sbarabe/SBK_WRISTBLASTER/images/Arm braced 24seg BarMeter PowerCell Battery pack holder (2).jpg

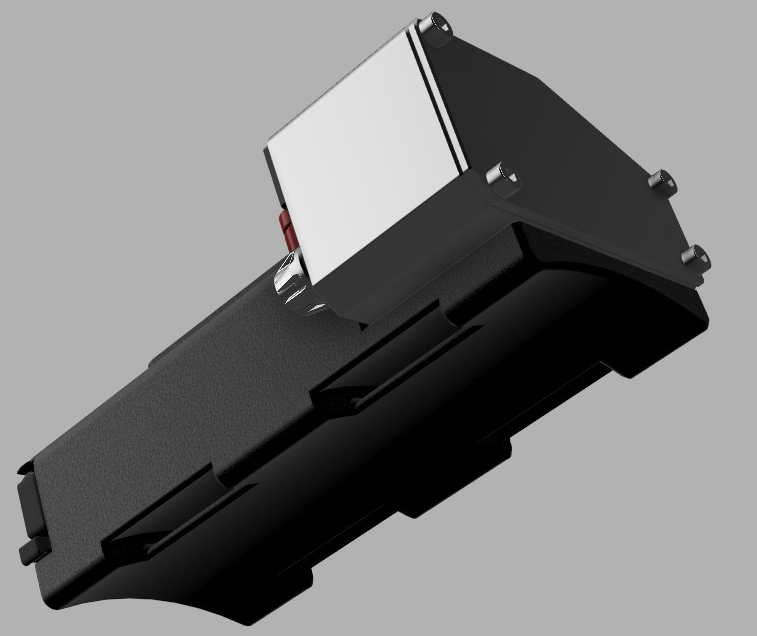
images/Arm braced 24seg BarMeter PowerCell Battery pack holder (2).jpg
