sbarabe/SBK_WRISTBLASTER/Schematics/SBK PCBs/SBK BarDrive SA28 V2.png

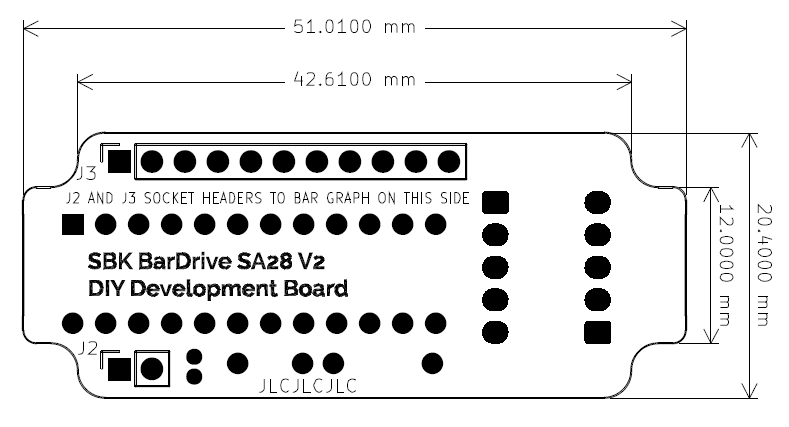
Schematics/SBK PCBs/SBK BarDrive SA28 V2.png
