sbarabe/SBK_WRISTBLASTER/Schematics/SBK PCBs/SBK BarDriveHT 28 V2.png

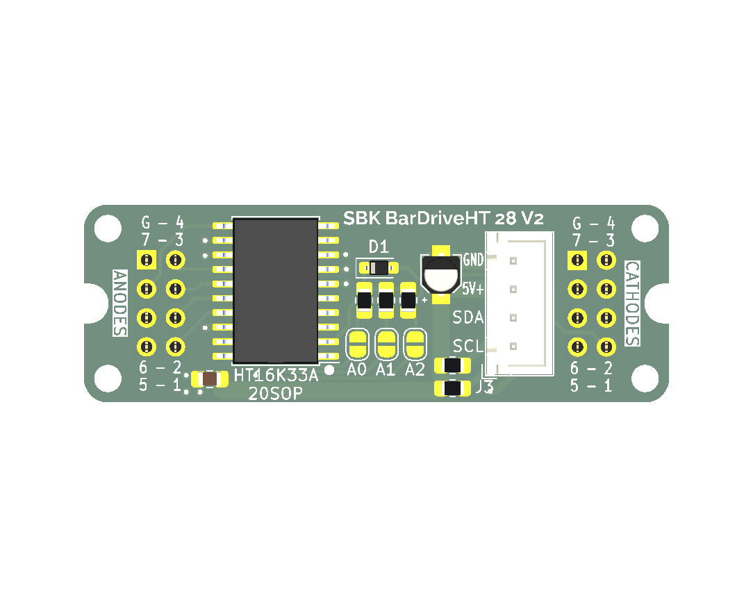
Schematics/SBK PCBs/SBK BarDriveHT 28 V2.png
