sbarabe/SBK_WRISTBLASTER/Schematics/SBK PCBs/SBK BarMeter SA28 V1.png

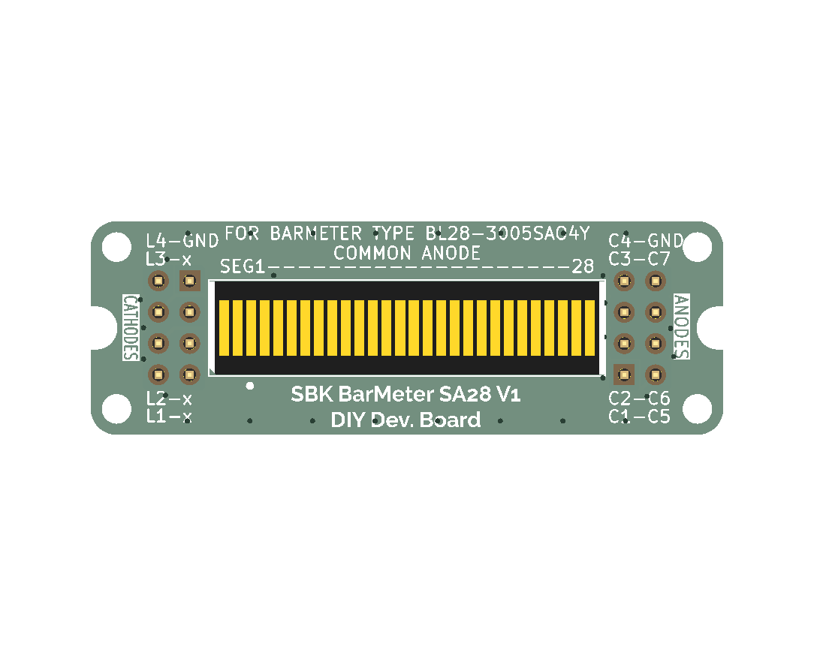
Schematics/SBK PCBs/SBK BarMeter SA28 V1.png
