sbarabe/SBK_WRISTBLASTER/3D model/V1 - 20250310/02.3-Gunbox Bar graph support.stl

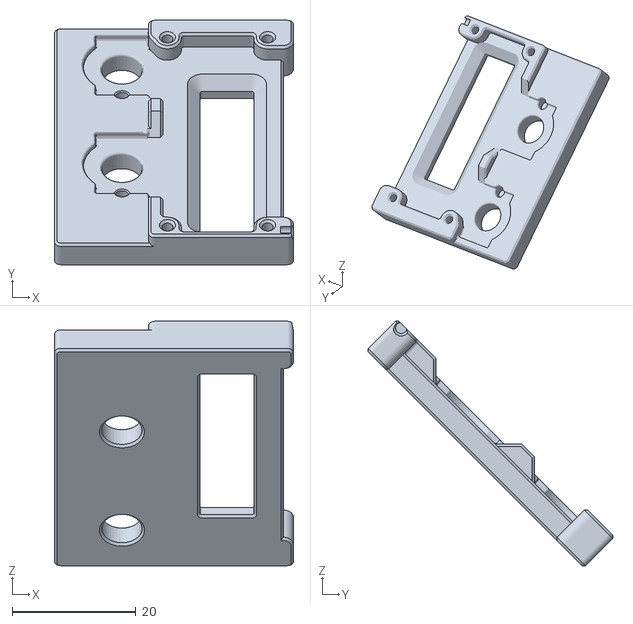
[picture p34: CAD file, 2025-04-01]
3D model/V1 - 20250310/02.3-Gunbox Bar graph support.stl
38.7 x 39.6 x 39.6
