sbarabe/SBK_WRISTBLASTER/3D model/V2 - 20260806/17A-Clippart valve body.stl

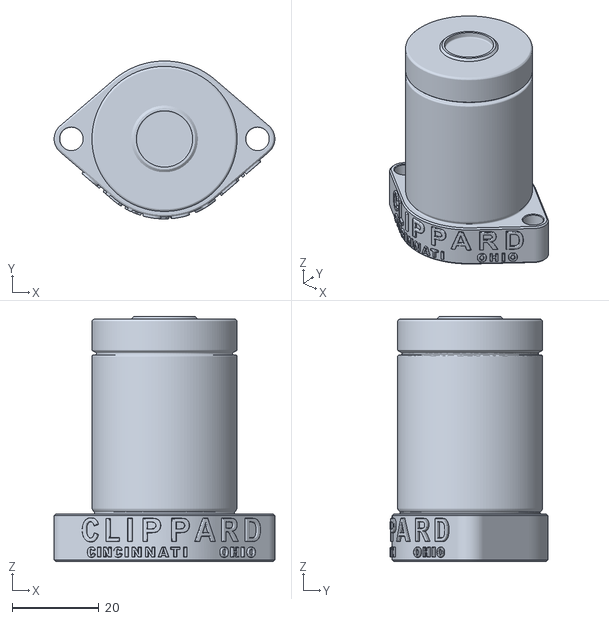
[picture p35: CAD file, 2026-08-06]
3D model/V2 - 20260806/17A-Clippart valve body.stl
51.0 x 36.5 x 56.6
