sbarabe/SBK_WRISTBLASTER/3D model/Battery pack holders/31.2B Battery pack holder COVER.stl

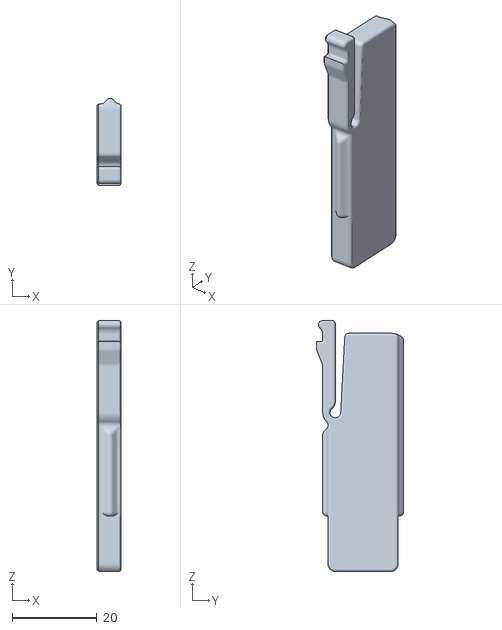
[picture p36: CAD file, 2025-04-04]
3D model/Battery pack holders/31.2B Battery pack holder COVER.stl
5.70 x 20.6 x 59.3
