sbarabe/SBK_WRISTBLASTER/3D model/V1 - 20250310/02-Gunbox ONE PIECE.stl

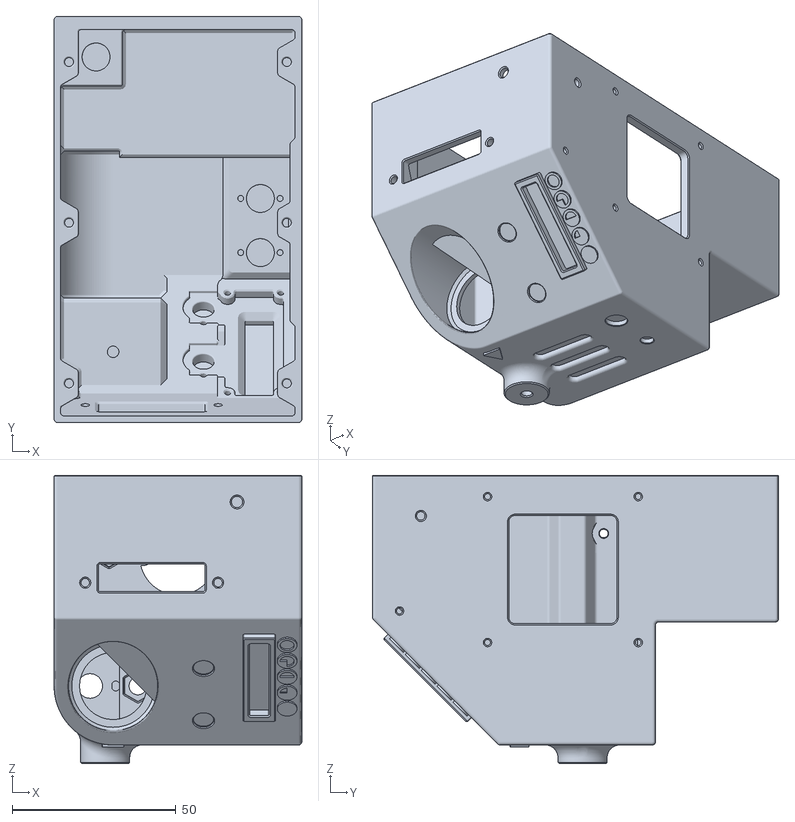
[picture p37: CAD file, 2025-03-19]
3D model/V1 - 20250310/02-Gunbox ONE PIECE.stl
75.6 x 123.8 x 87.9
