sbarabe/SBK_WRISTBLASTER/3D model/V2 - 20260806/18A-Clippart valve knob.stl

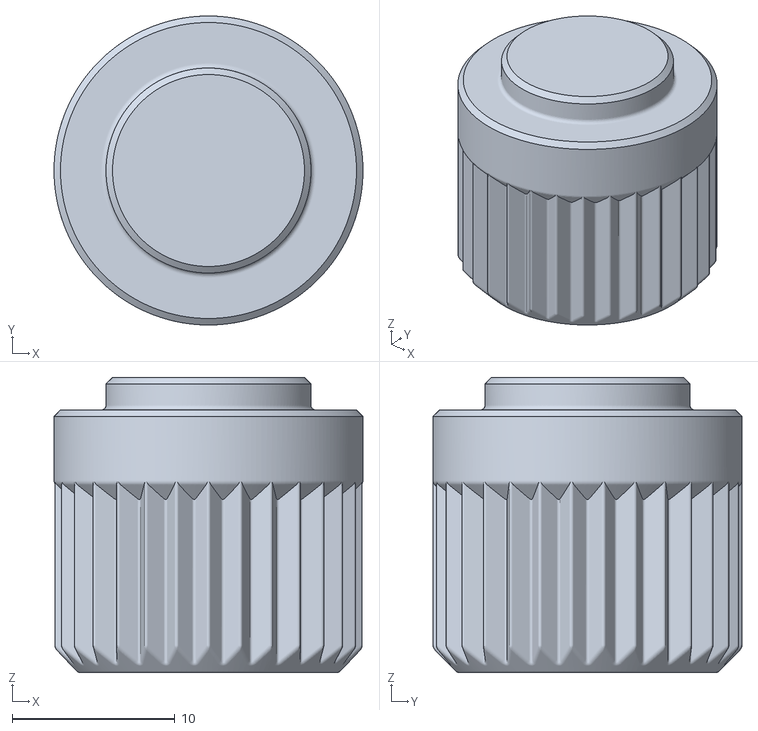
[picture p38: CAD file, 2026-08-06]
3D model/V2 - 20260806/18A-Clippart valve knob.stl
19.0 x 19.0 x 18.2
