sbarabe/SBK_WRISTBLASTER/3D model/Battery pack holders/31.4B_C Cable gland.stl

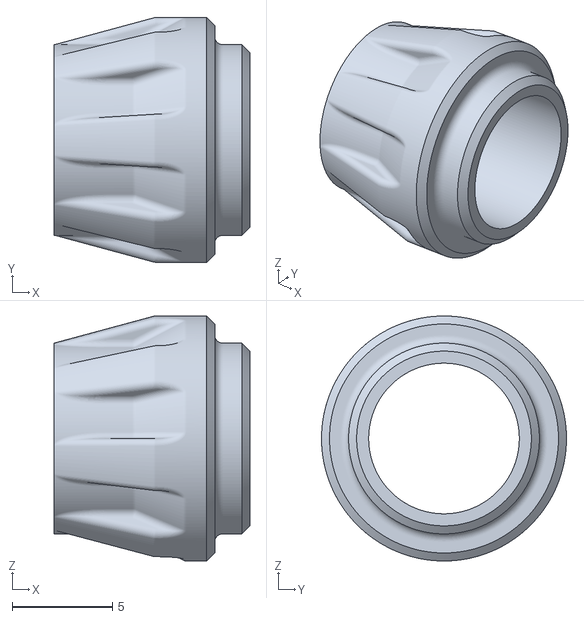
[picture p39: CAD file, 2025-04-04]
3D model/Battery pack holders/31.4B_C Cable gland.stl
9.75 x 12.2 x 12.2
