sbarabe/SBK_WRISTBLASTER/3D model/V1 - 20250310/02.1-Gunbox.stl

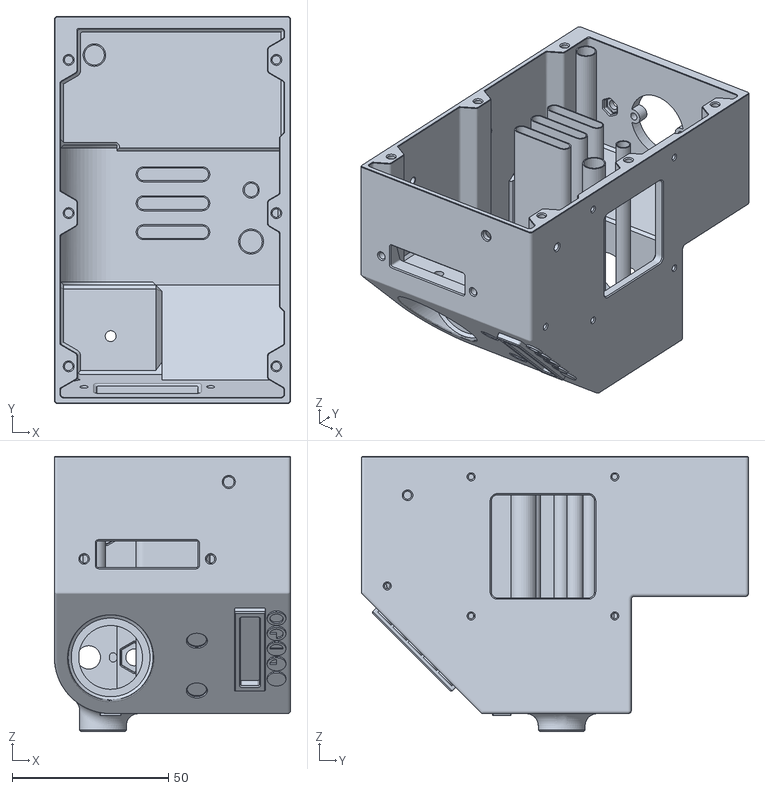
[picture p40: CAD file, 2025-03-12]
3D model/V1 - 20250310/02.1-Gunbox.stl
75.6 x 123.8 x 87.9
