sbarabe/SBK_WRISTBLASTER/3D model/V1 - 20250310/25B-Fire Handle body .375 copper tube.stl

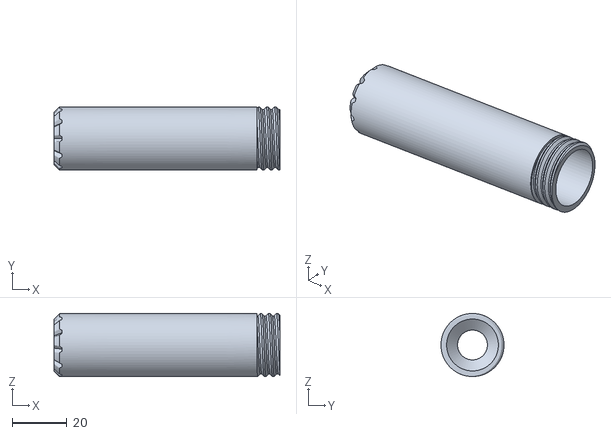
[picture p41: CAD file, 2025-03-10]
3D model/V1 - 20250310/25B-Fire Handle body .375 copper tube.stl
82.8 x 23.1 x 23.1
