sbarabe/SBK_WRISTBLASTER/3D model/V2 - 20260806/18B-Clippart valve knob for potentiometer V2.stl

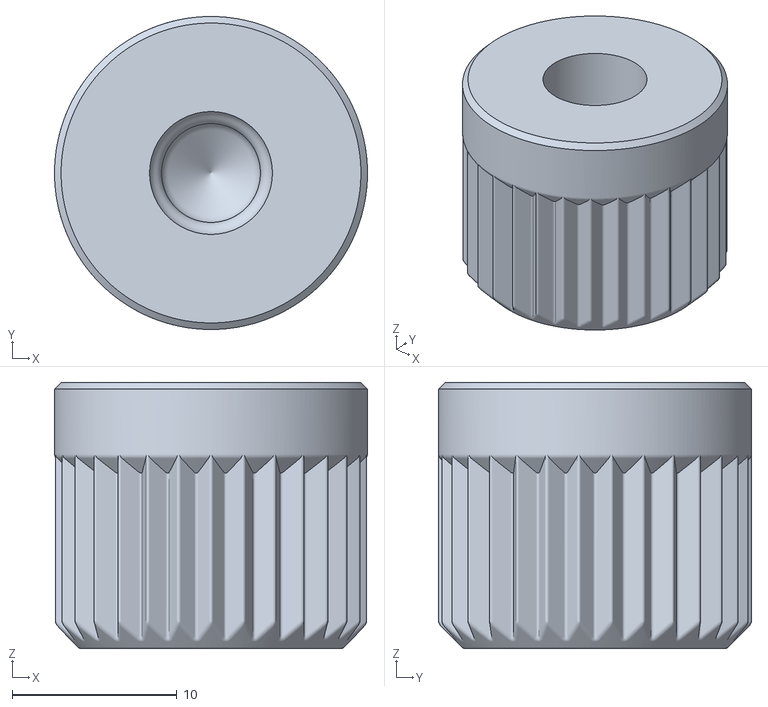
[picture p42: CAD file, 2026-08-06]
3D model/V2 - 20260806/18B-Clippart valve knob for potentiometer V2.stl
19.0 x 19.0 x 16.2
