sbarabe/SBK_WRISTBLASTER/3D model/Battery pack holders/31.3B Powercell switch back cover.stl

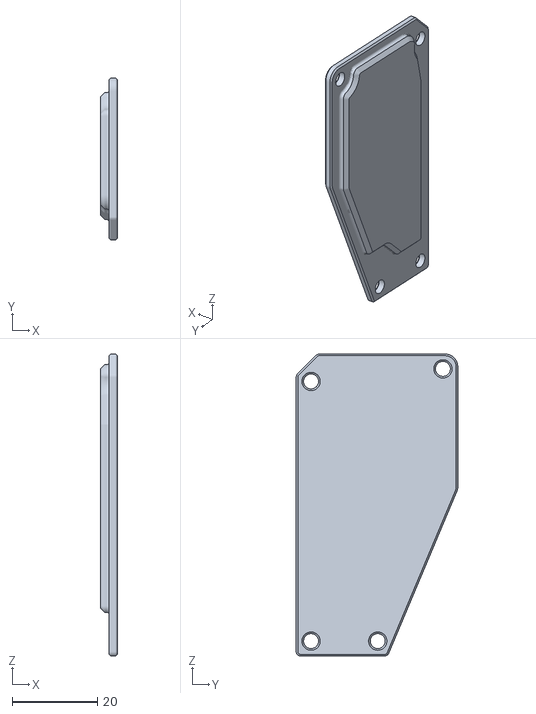
[picture p43: CAD file, 2025-04-04]
3D model/Battery pack holders/31.3B Powercell switch back cover.stl
4.00 x 38.0 x 71.0
