sbarabe/SBK_WRISTBLASTER/3D model/V1 - 20250310/02.2-Gunbox top indicators leds support.stl

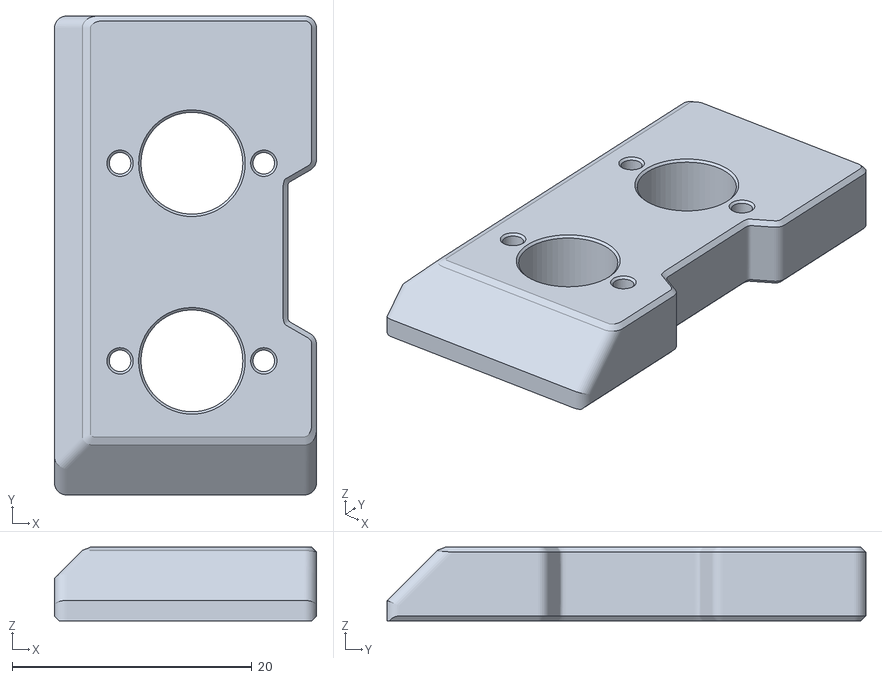
[picture p44: CAD file, 2025-03-10]
3D model/V1 - 20250310/02.2-Gunbox top indicators leds support.stl
21.9 x 40.0 x 6.15
