sbarabe/SBK_WRISTBLASTER/3D model/V2 - 20260806/17B-Clippart valve body for potentiometer V2.stl

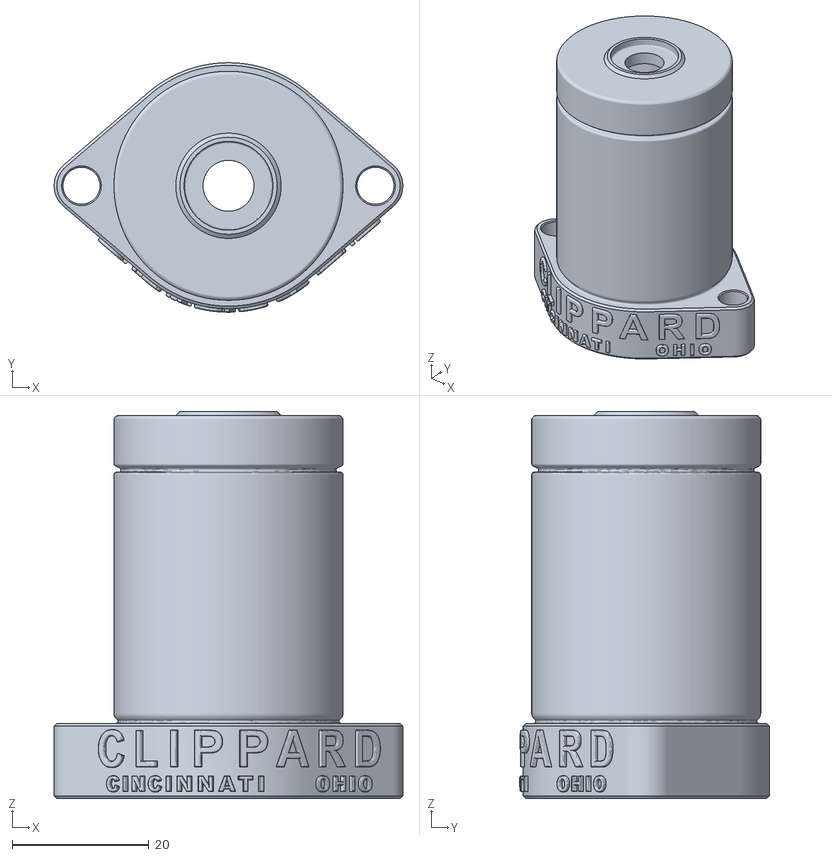
[picture p45: CAD file, 2026-08-06]
3D model/V2 - 20260806/17B-Clippart valve body for potentiometer V2.stl
51.0 x 36.5 x 56.6
