sbarabe/SBK_WRISTBLASTER/3D model/Battery pack holders/31.6B Powercell 9x57x2mm lens (clear or frosted acrylic, not to be printed).stl

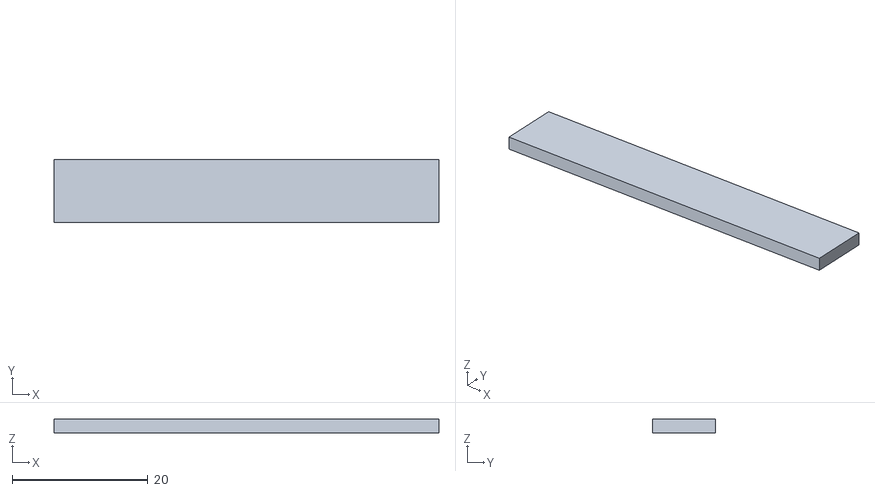
[picture p46: CAD file, 2025-03-24]
3D model/Battery pack holders/31.6B Powercell 9x57x2mm lens (clear or frosted acrylic, not to be printed).stl
56.8 x 9.30 x 2.00
