sbarabe/SBK_WRISTBLASTER/3D model/V2 - 20260806/04-Arm brace LARGE V2 - one side version.stl

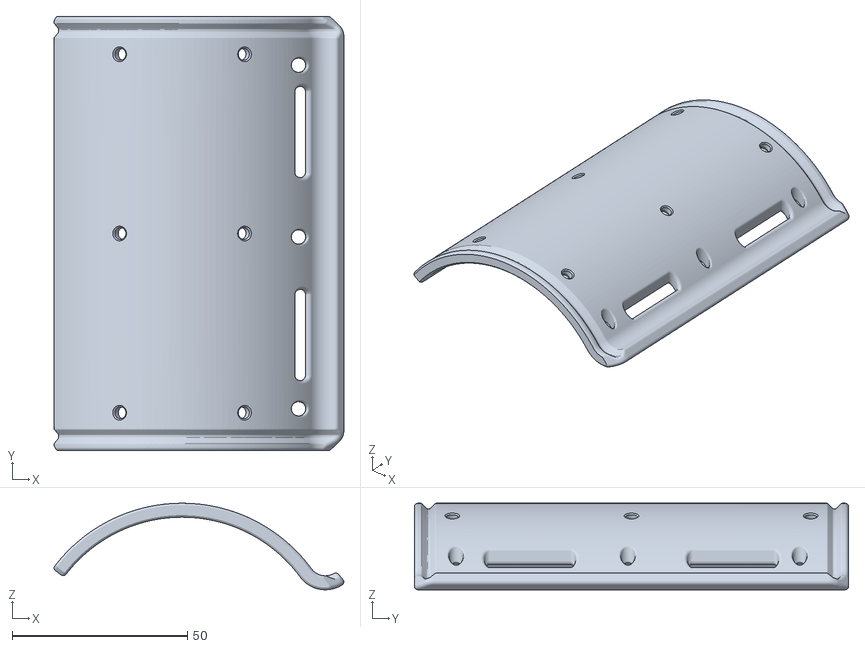
[picture p47: CAD file, 2026-08-06]
3D model/V2 - 20260806/04-Arm brace LARGE V2 - one side version.stl
82.6 x 123.8 x 24.7
