sbarabe/SBK_WRISTBLASTER/3D model/V1 - 20250310/02.4-Gunbox Front indicator led support.stl

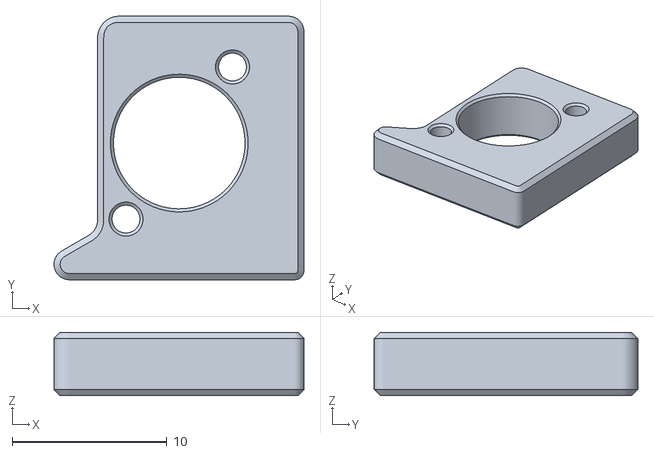
[picture p48: CAD file, 2025-03-10]
3D model/V1 - 20250310/02.4-Gunbox Front indicator led support.stl
16.2 x 17.0 x 4.10
