sbarabe/SBK_WRISTBLASTER/3D model/V2 - 20260806/04-Arm brace LARGE V2 - symetric.stl

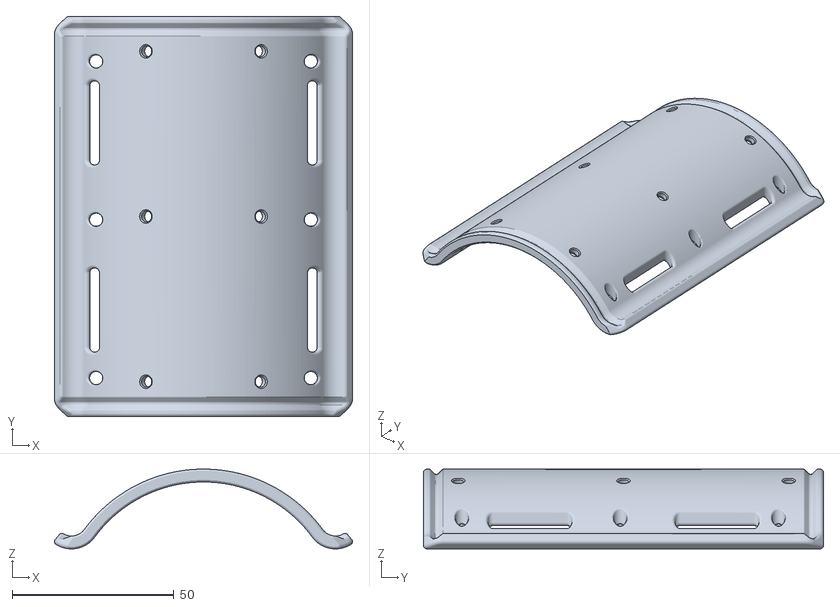
[picture p49: CAD file, 2026-08-06]
3D model/V2 - 20260806/04-Arm brace LARGE V2 - symetric.stl
92.3 x 123.8 x 24.7
