sbarabe/SBK_WRISTBLASTER/3D model/V1 - 20250310/27-Fire rod lens holder.stl

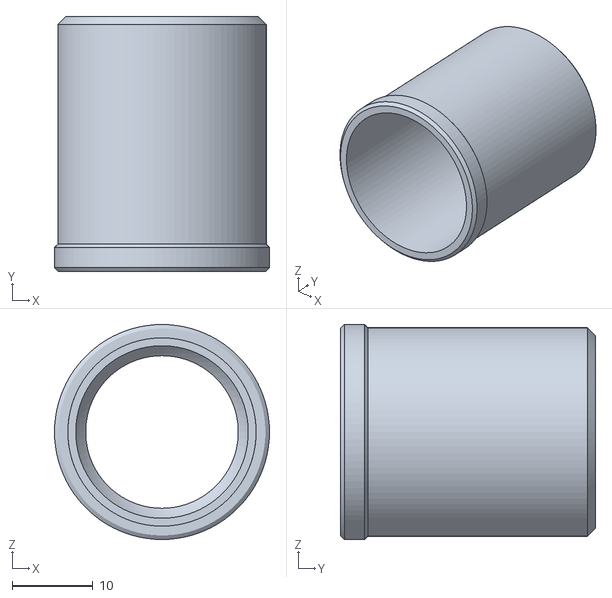
[picture p51: CAD file, 2025-03-10]
3D model/V1 - 20250310/27-Fire rod lens holder.stl
26.6 x 31.6 x 26.6
