sbarabe/SBK_WRISTBLASTER/3D model/V2 - 20260806/33 Handle V2 (38 copper tubing for reference).stl

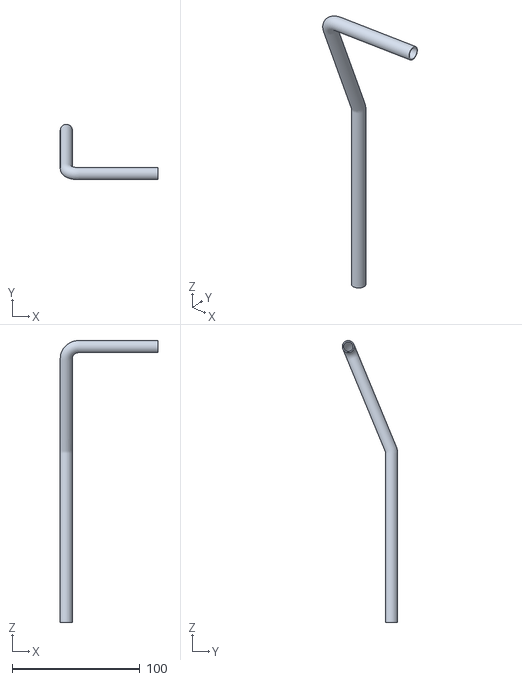
[picture p52: CAD file, 2026-08-06]
3D model/V2 - 20260806/33 Handle V2 (38 copper tubing for reference).stl
76.4 x 43.4 x 220.8
