sbarabe/SBK_WRISTBLASTER/3D model/V1 - 20250310/04-Arm brace D version.stl

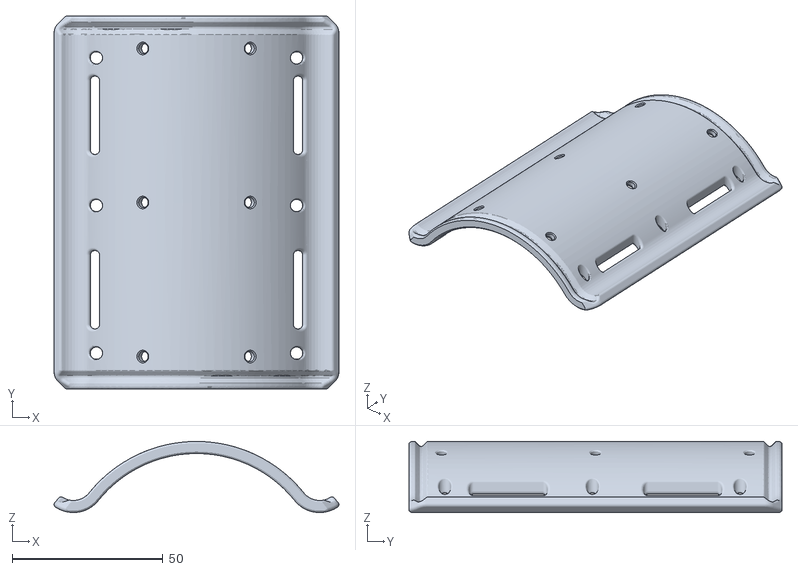
[picture p53: CAD file, 2025-03-10]
3D model/V1 - 20250310/04-Arm brace D version.stl
94.5 x 123.8 x 23.6
