sbarabe/SBK_WRISTBLASTER/3D model/V2 - 20260806/25-Fire Handle body V2 (3_8 copper tube).stl

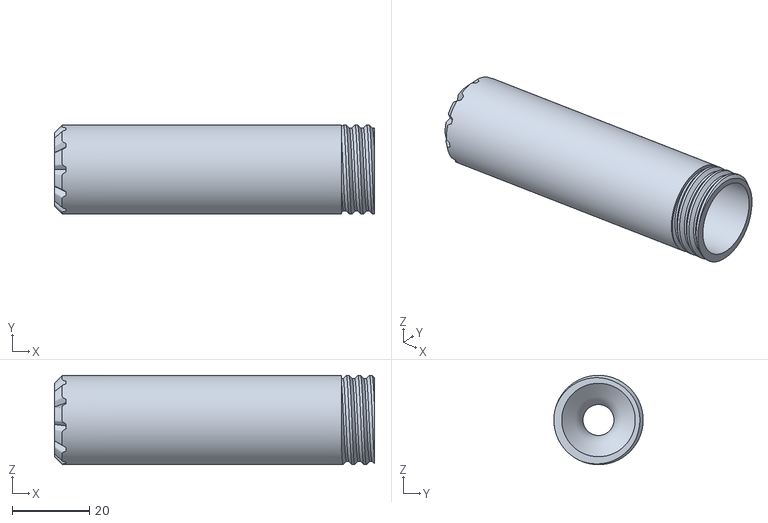
[picture p54: CAD file, 2026-08-06]
3D model/V2 - 20260806/25-Fire Handle body V2 (3_8 copper tube).stl
82.8 x 23.1 x 23.1
