sbarabe/SBK_WRISTBLASTER/3D model/V1 - 20250310/29-Vent lens.stl

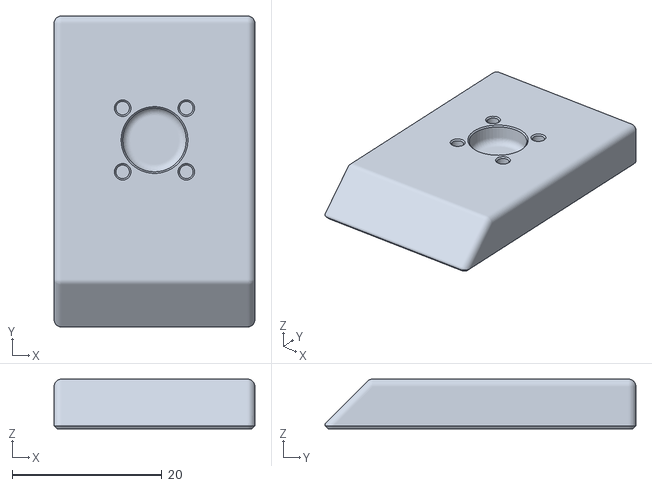
[picture p55: CAD file, 2025-03-10]
3D model/V1 - 20250310/29-Vent lens.stl
26.8 x 41.5 x 6.65
