sbarabe/SBK_WRISTBLASTER/3D model/V2 - 20260806/27-Fire rod lens holder V2.stl

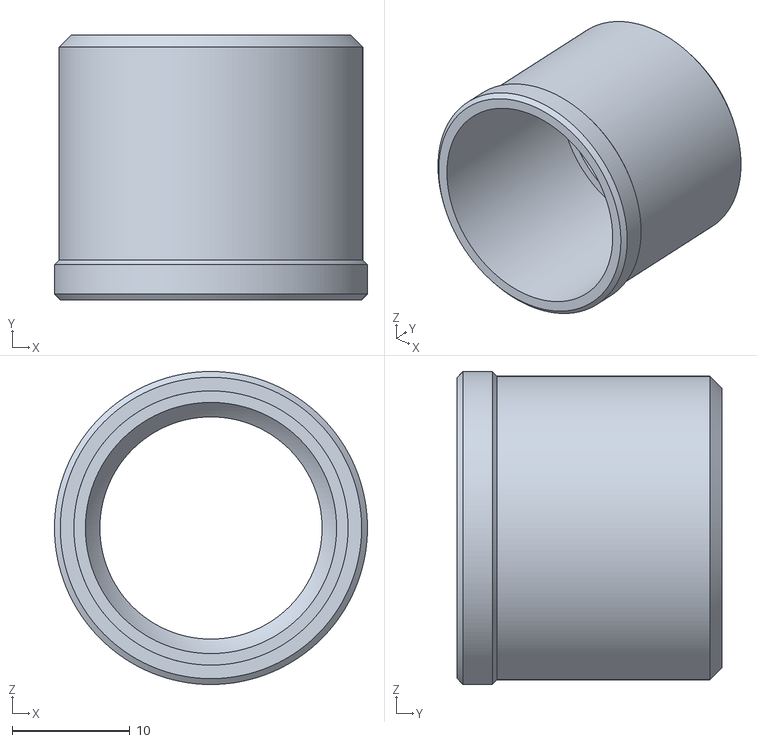
[picture p56: CAD file, 2026-08-06]
3D model/V2 - 20260806/27-Fire rod lens holder V2.stl
26.6 x 22.5 x 26.6
