sbarabe/SBK_WRISTBLASTER/3D model/V1 - 20250310/04-Arm brace D-trunk version.stl

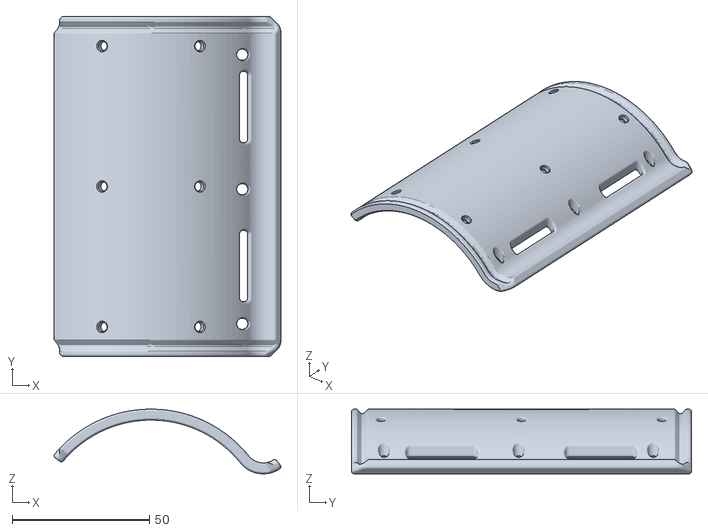
[picture p57: CAD file, 2025-03-10]
3D model/V1 - 20250310/04-Arm brace D-trunk version.stl
82.5 x 123.8 x 23.6
