sbarabe/SBK_WRISTBLASTER/3D model/V1 - 20250310/22B-Gunbox Heatsink with fan.stl

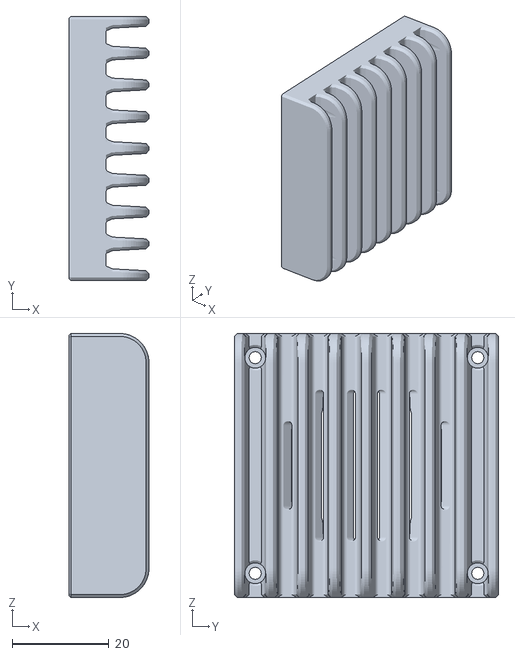
[picture p58: CAD file, 2025-03-10]
3D model/V1 - 20250310/22B-Gunbox Heatsink with fan.stl
16.5 x 54.5 x 54.5
