sbarabe/SBK_WRISTBLASTER/3D model/V2 - 20260806/29-Vent lens V2.stl

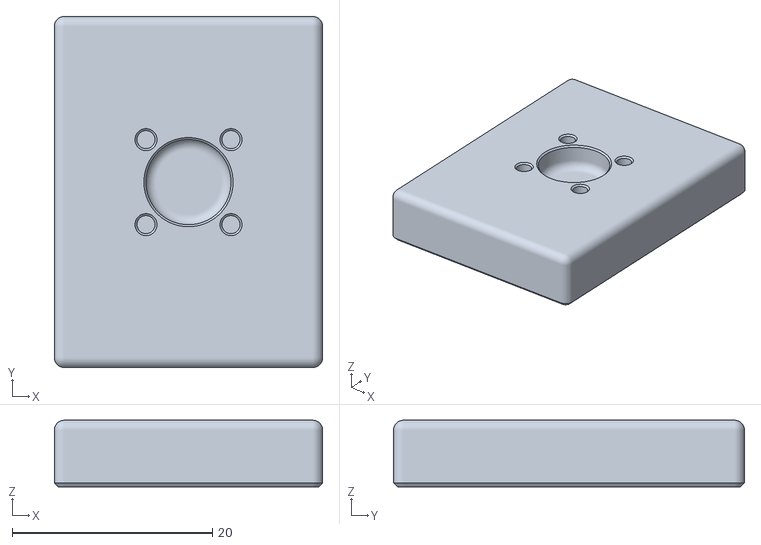
[picture p60: CAD file, 2025-11-30]
3D model/V2 - 20260806/29-Vent lens V2.stl
26.8 x 35.0 x 6.65
