sbarabe/SBK_WRISTBLASTER/3D model/V2 - 20260806/05-Gunbox front panel.stl

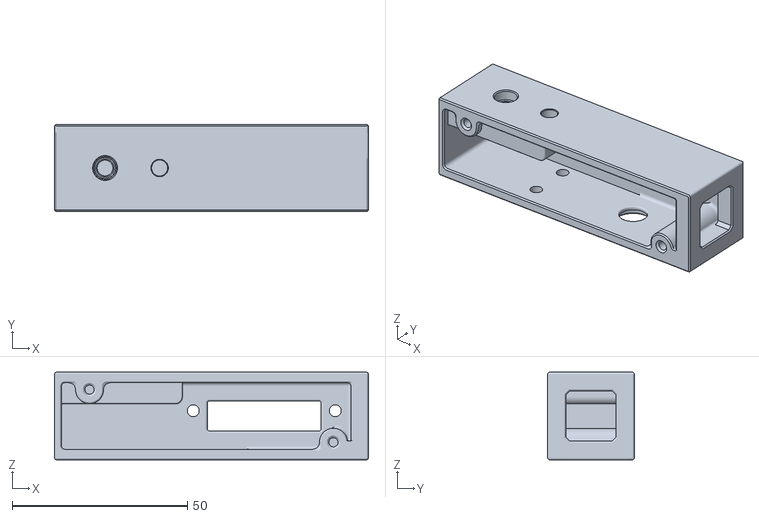
[picture p61: CAD file, 2025-11-03]
3D model/V2 - 20260806/05-Gunbox front panel.stl
89.6 x 24.9 x 25.0
