sbarabe/SBK_WRISTBLASTER/3D model/V2 - 20260806/19B.1-Mini cyclotron tube 95mm (longer for smoke device).stl

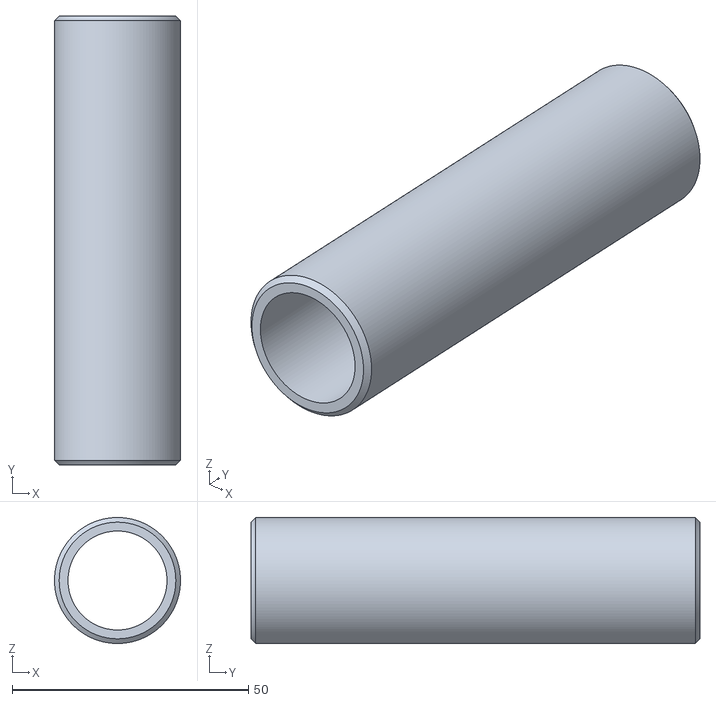
[picture p62: CAD file, 2025-04-04]
3D model/V2 - 20260806/19B.1-Mini cyclotron tube 95mm (longer for smoke device).stl
26.7 x 95.0 x 26.7
