sbarabe/SBK_WRISTBLASTER/3D model/V2 - 20260806/19C-Mini cyclotron tube 80mm with ring.stl

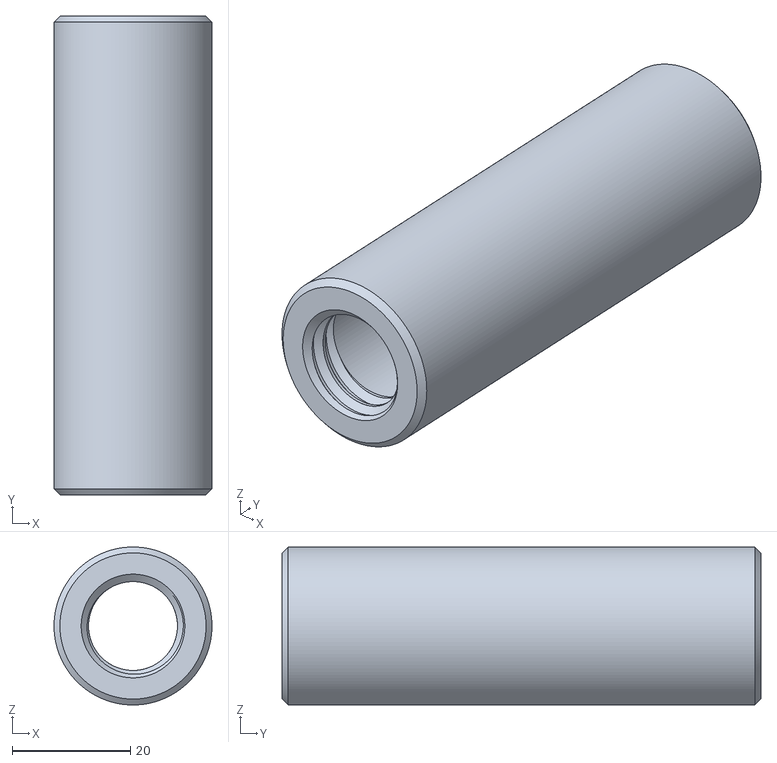
[picture p63: CAD file, 2025-04-04]
3D model/V2 - 20260806/19C-Mini cyclotron tube 80mm with ring.stl
26.7 x 80.8 x 26.7
