sbarabe/SBK_WRISTBLASTER/3D model/V2 - 20260806/19.2A_.2B-Cyclotron tube filets ring.stl

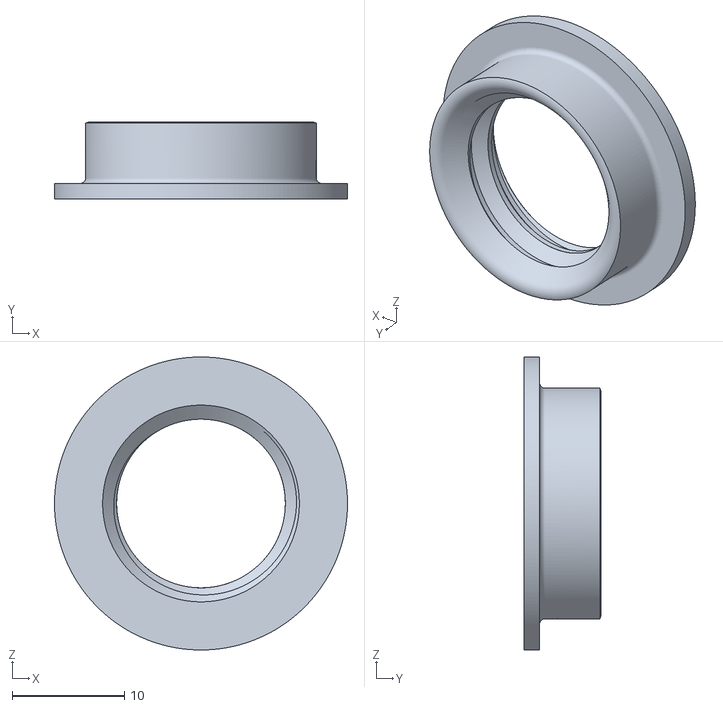
[picture p64: CAD file, 2025-04-04]
3D model/V2 - 20260806/19.2A_.2B-Cyclotron tube filets ring.stl
26.1 x 6.88 x 26.1
