sbarabe/SBK_WRISTBLASTER/3D model/V2 - 20260806/07A-Gunbox front side panel with activate push button.stl

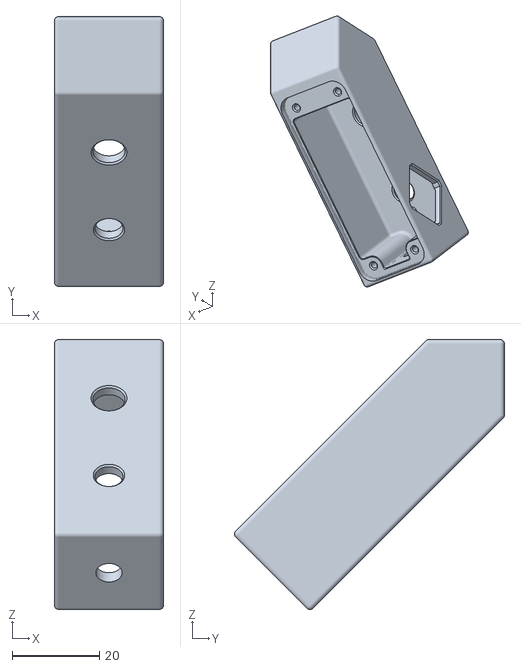
[picture p65: CAD file, 2025-03-19]
3D model/V2 - 20260806/07A-Gunbox front side panel with activate push button.stl
25.0 x 61.8 x 61.8
