sbarabe/SBK_WRISTBLASTER/3D model/V2 - 20260806/06-Gunbox front panel cover.stl

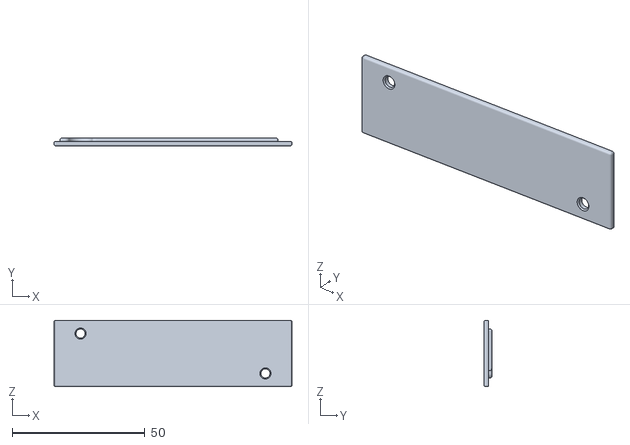
[picture p66: CAD file, 2025-03-10]
3D model/V2 - 20260806/06-Gunbox front panel cover.stl
89.6 x 3.00 x 25.0
