sbarabe/SBK_WRISTBLASTER/3D model/V2 - 20260806/11-Gunbox front valve.stl

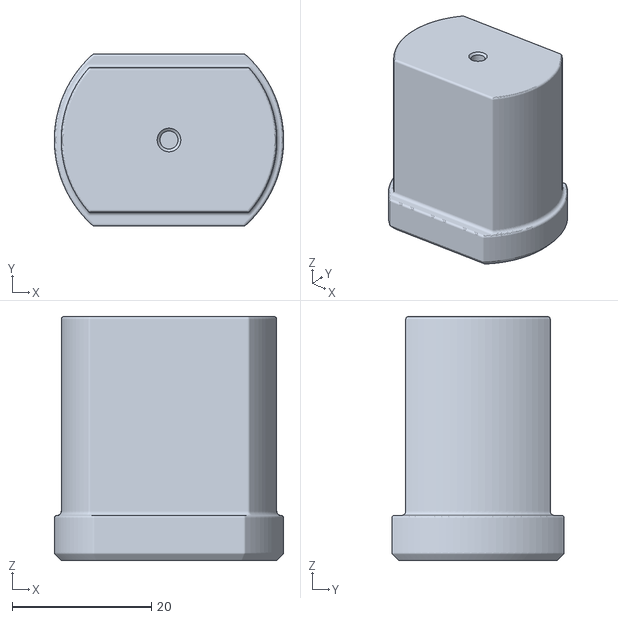
[picture p67: CAD file, 2025-03-10]
3D model/V2 - 20260806/11-Gunbox front valve.stl
33.0 x 24.8 x 35.1
