sbarabe/SBK_WRISTBLASTER/3D model/V2 - 20260806/10.2-Front guard quarter side 1.stl

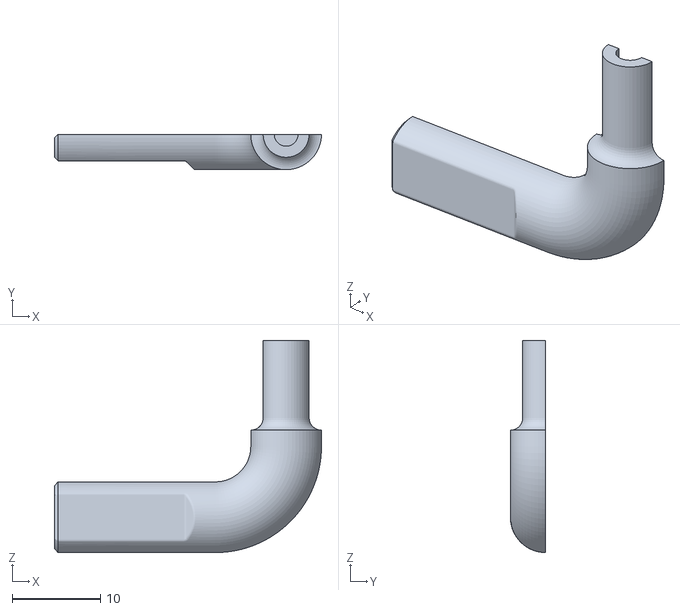
[picture p68: CAD file, 2025-03-10]
3D model/V2 - 20260806/10.2-Front guard quarter side 1.stl
30.2 x 4.00 x 24.0
