sbarabe/SBK_WRISTBLASTER/3D model/V2 - 20260806/08-Gunbox front side panel bottom.stl

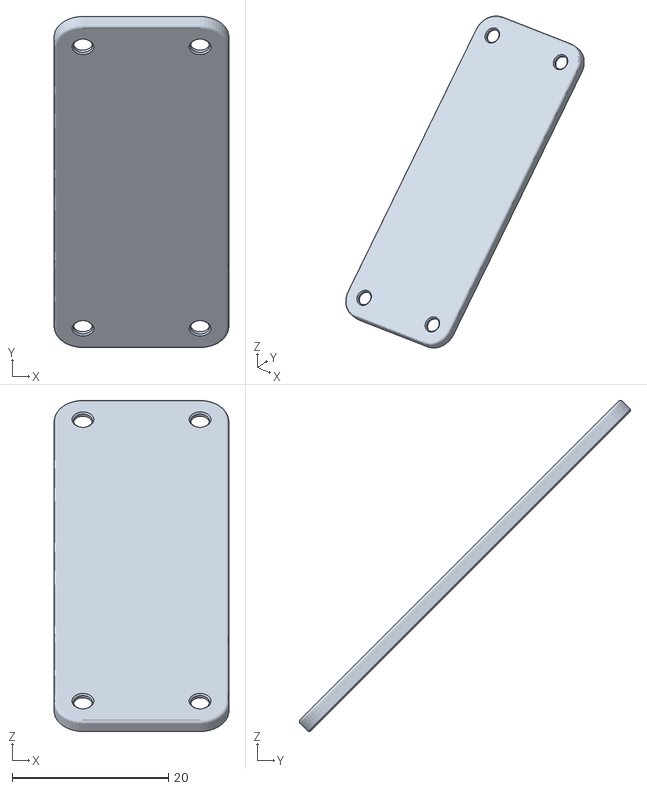
[picture p69: CAD file, 2025-03-10]
3D model/V2 - 20260806/08-Gunbox front side panel bottom.stl
22.4 x 42.4 x 42.4
