sbarabe/SBK_WRISTBLASTER/3D model/V2 - 20260806/13-Gunbox side double knob.stl

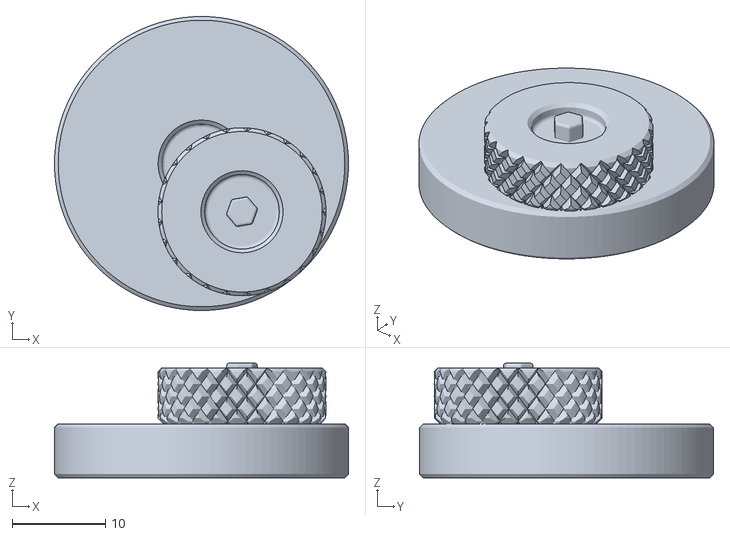
[picture p70: CAD file, 2025-03-10]
3D model/V2 - 20260806/13-Gunbox side double knob.stl
31.5 x 31.5 x 12.3
