sbarabe/SBK_WRISTBLASTER/3D model/V2 - 20260806/22A-Gunbox Heatsink.stl

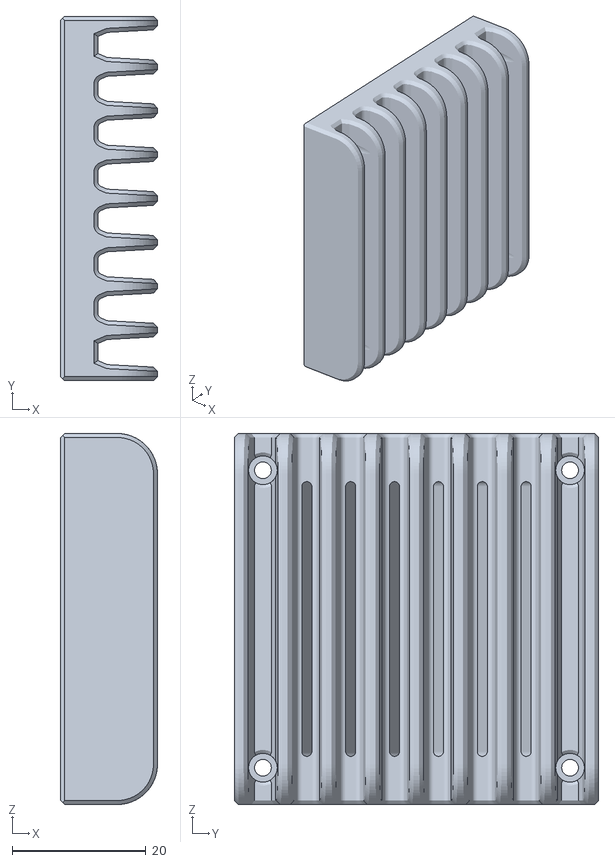
[picture p71: CAD file, 2025-03-10]
3D model/V2 - 20260806/22A-Gunbox Heatsink.stl
14.5 x 54.5 x 55.5
