sbarabe/SBK_WRISTBLASTER/3D model/V2 - 20260806/19A.1-Mini cyclotron tube 80mm.stl

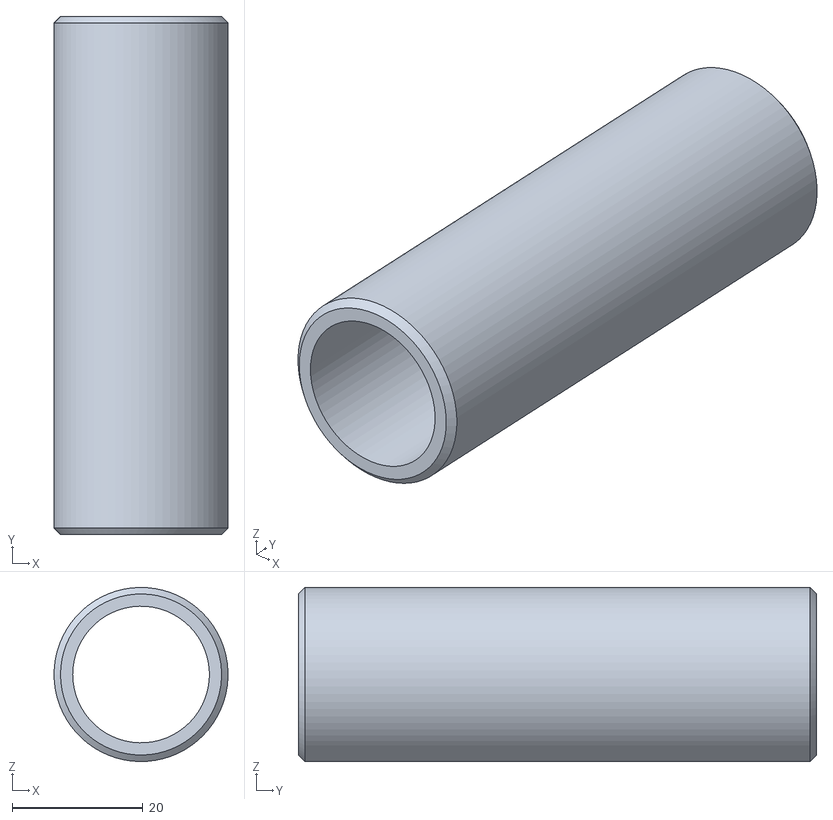
[picture p72: CAD file, 2025-03-10]
3D model/V2 - 20260806/19A.1-Mini cyclotron tube 80mm.stl
26.7 x 79.4 x 26.7
