sbarabe/SBK_WRISTBLASTER/3D model/V2 - 20260806/10-Front guard ONE PIECE.stl

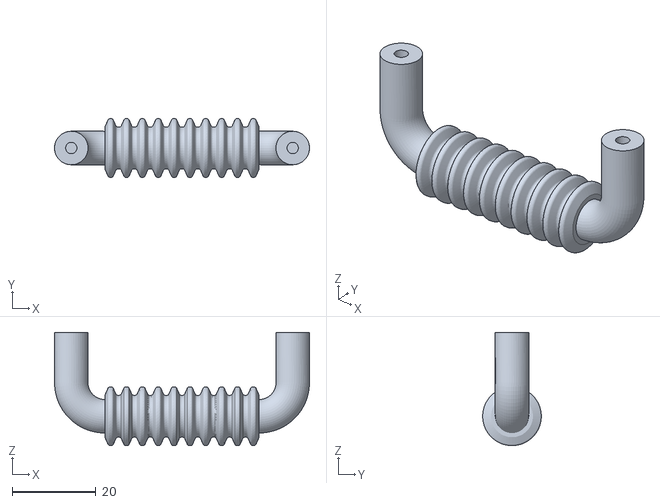
[picture p73: CAD file, 2025-03-10]
3D model/V2 - 20260806/10-Front guard ONE PIECE.stl
60.8 x 14.0 x 27.0
