sbarabe/SBK_WRISTBLASTER/3D model/V2 - 20260806/09-Gunbox front panel side connector.stl

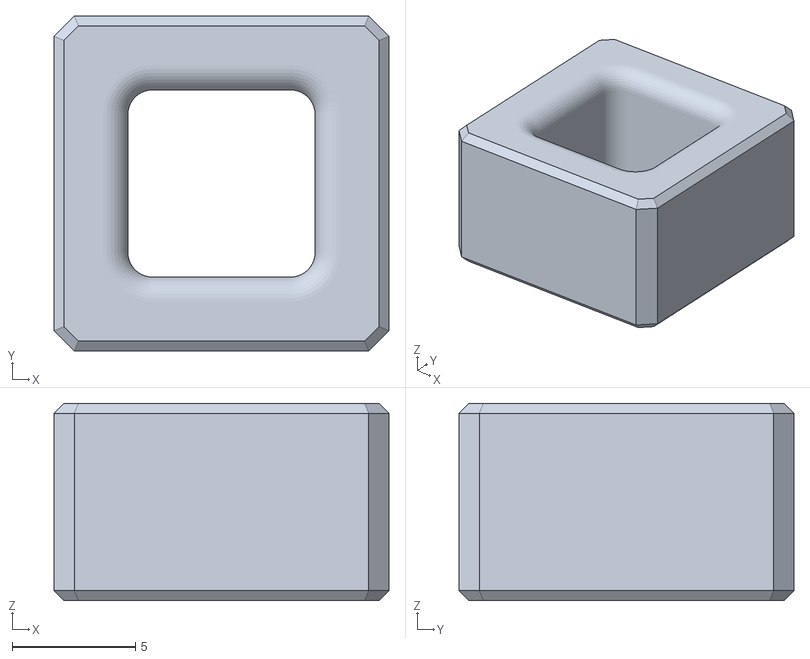
[picture p74: CAD file, 2025-03-10]
3D model/V2 - 20260806/09-Gunbox front panel side connector.stl
13.6 x 13.6 x 8.00
