sbarabe/SBK_WRISTBLASTER/3D model/V2 - 20260806/12-Gunbox back panel POT knob.stl

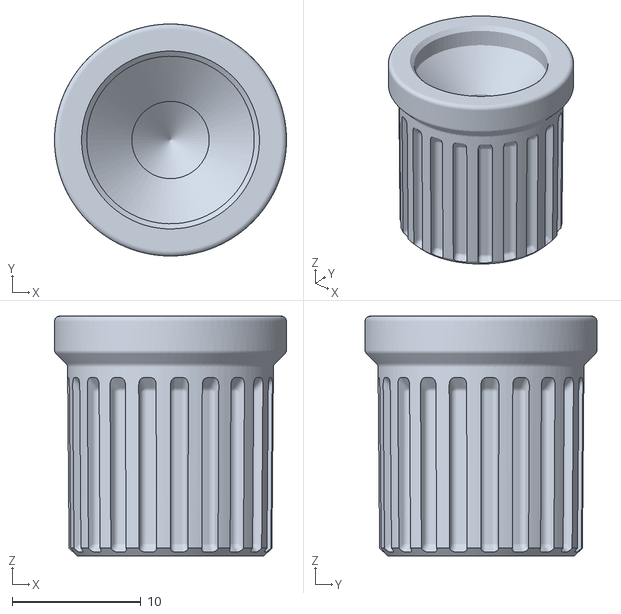
[picture p75: CAD file, 2025-03-10]
3D model/V2 - 20260806/12-Gunbox back panel POT knob.stl
18.0 x 18.0 x 18.6
