sbarabe/SBK_WRISTBLASTER/3D model/V2 - 20260806/16-Gunbox top knob.stl

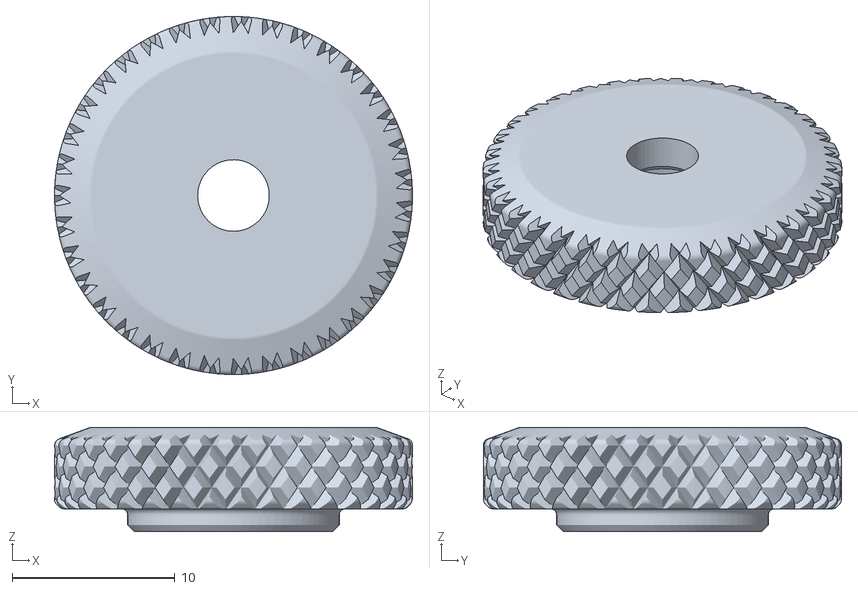
[picture p76: CAD file, 2025-03-10]
3D model/V2 - 20260806/16-Gunbox top knob.stl
22.0 x 22.0 x 6.40
