sbarabe/SBK_WRISTBLASTER/3D model/V2 - 20260806/28-Pneumatic fitting slim.stl

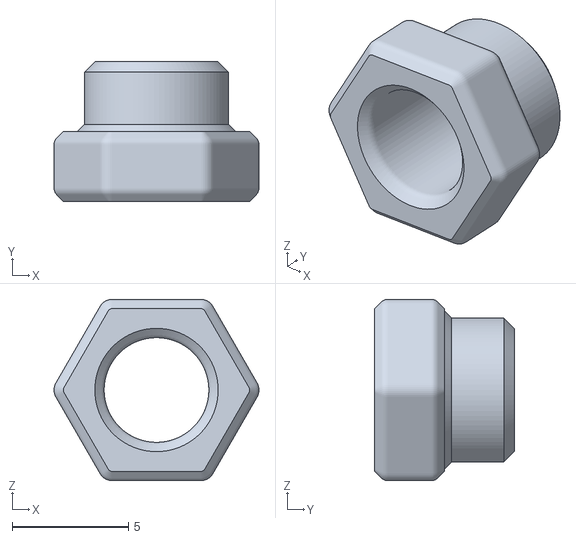
[picture p77: CAD file, 2025-03-10]
3D model/V2 - 20260806/28-Pneumatic fitting slim.stl
8.81 x 6.00 x 7.79
