sbarabe/SBK_WRISTBLASTER/3D model/V2 - 20260806/26-strob lens 23mm (reference).stl

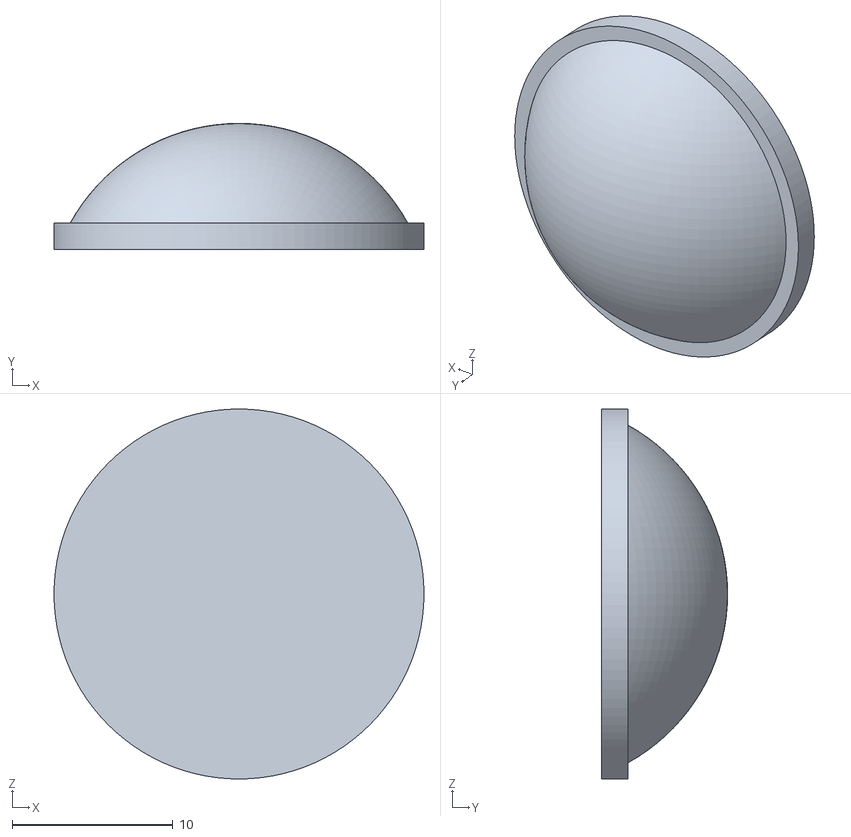
[picture p78: CAD file, 2025-03-10]
3D model/V2 - 20260806/26-strob lens 23mm (reference).stl
23.0 x 7.85 x 23.0
