sbarabe/SBK_WRISTBLASTER/3D model/V2 - 20260806/10.4 Front Guard heat sink.stl

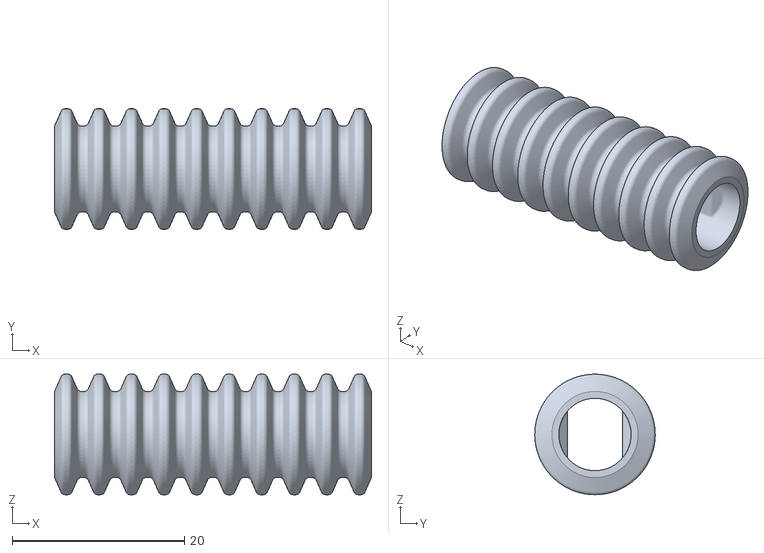
[picture p79: CAD file, 2025-03-10]
3D model/V2 - 20260806/10.4 Front Guard heat sink.stl
36.8 x 14.0 x 14.0
