sbarabe/SBK_WRISTBLASTER/3D model/V2 - 20260806/21-Mini Cyclotron lens cover.stl

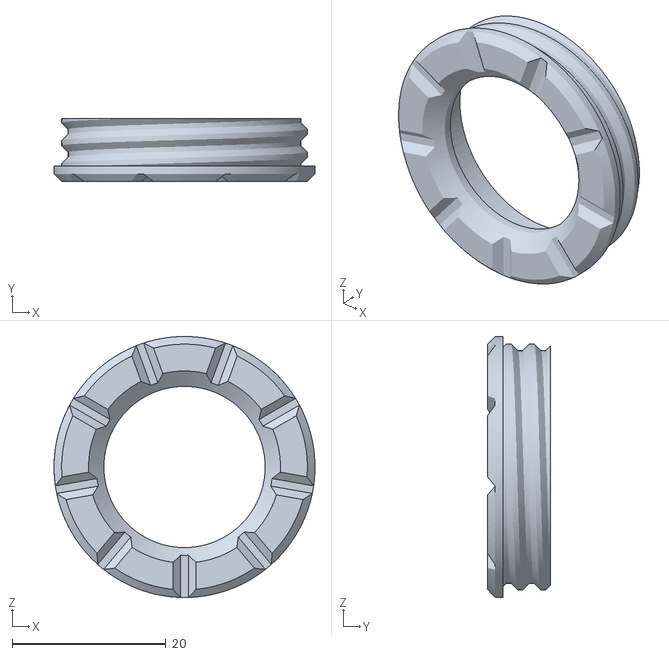
[picture p80: CAD file, 2025-03-10]
3D model/V2 - 20260806/21-Mini Cyclotron lens cover.stl
34.0 x 8.21 x 34.0
