sbarabe/SBK_WRISTBLASTER/3D model/V2 - 20260806/20-Mini cyclotron.stl

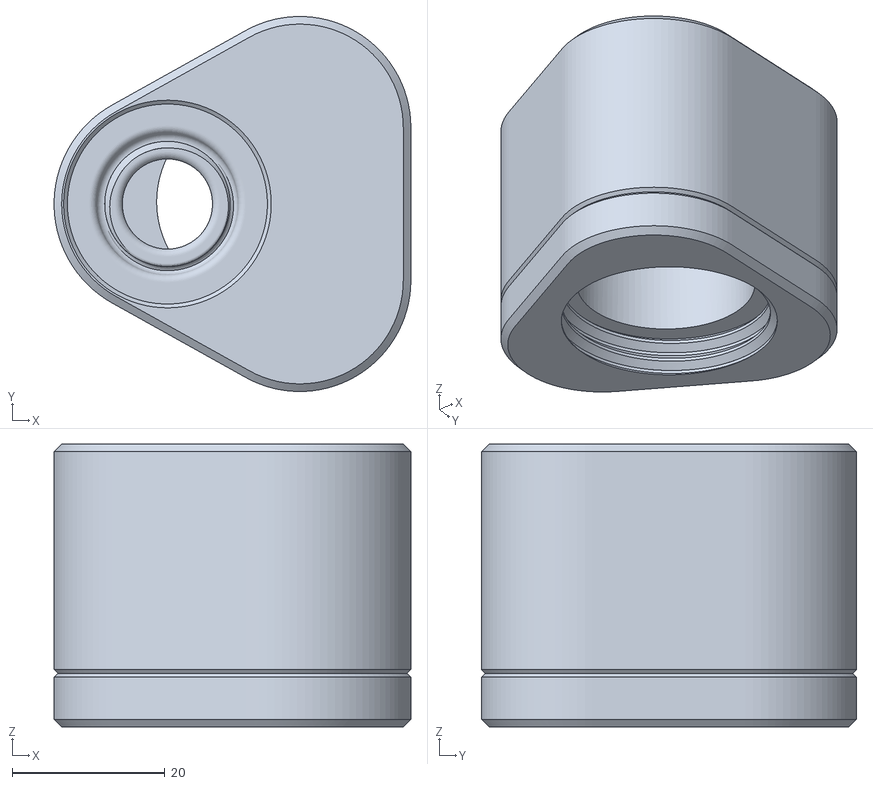
[picture p81: CAD file, 2025-03-10]
3D model/V2 - 20260806/20-Mini cyclotron.stl
46.7 x 49.1 x 37.0
