sbarabe/SBK_WRISTBLASTER/3D model/V2 - 20260806/23-Fire handlebutton cap.stl

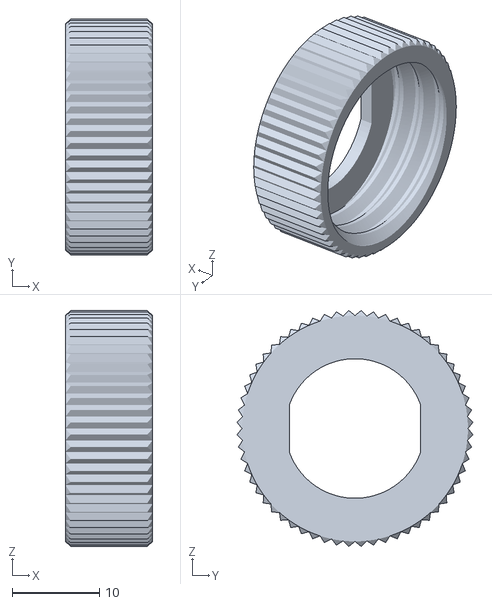
[picture p82: CAD file, 2025-03-10]
3D model/V2 - 20260806/23-Fire handlebutton cap.stl
10.0 x 27.1 x 27.1
