sbarabe/SBK_WRISTBLASTER/3D model/V2 - 20260806/30-Gunbox Side Panel Wire Clip.stl

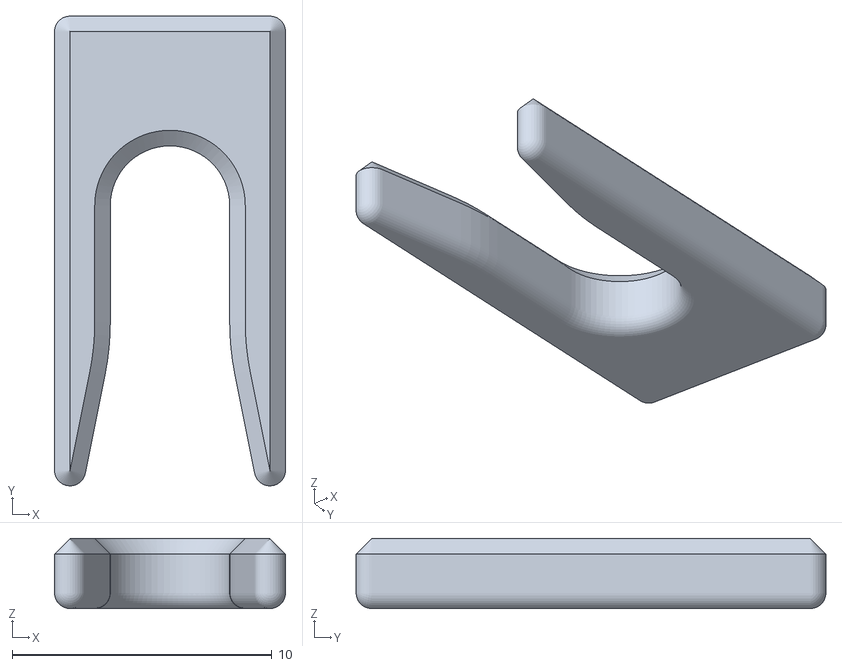
[picture p83: CAD file, 2025-03-10]
3D model/V2 - 20260806/30-Gunbox Side Panel Wire Clip.stl
8.90 x 18.1 x 2.70
