sbarabe/SBK_WRISTBLASTER/3D model/V2 - 20260806/10.1-Front guard sleeve.stl

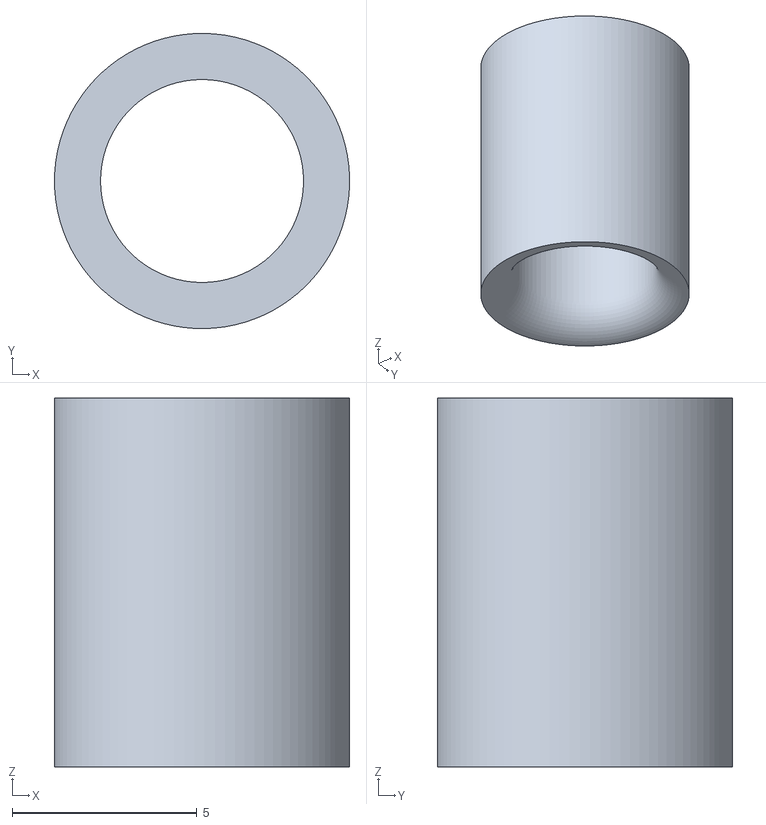
[picture p84: CAD file, 2025-03-10]
3D model/V2 - 20260806/10.1-Front guard sleeve.stl
8.00 x 8.00 x 10.0
